calvin-mcd/oceanographer-ec/Project/analog.kicad_sch

## KiCad design Project/analog.kicad_sch (2024-09-16)

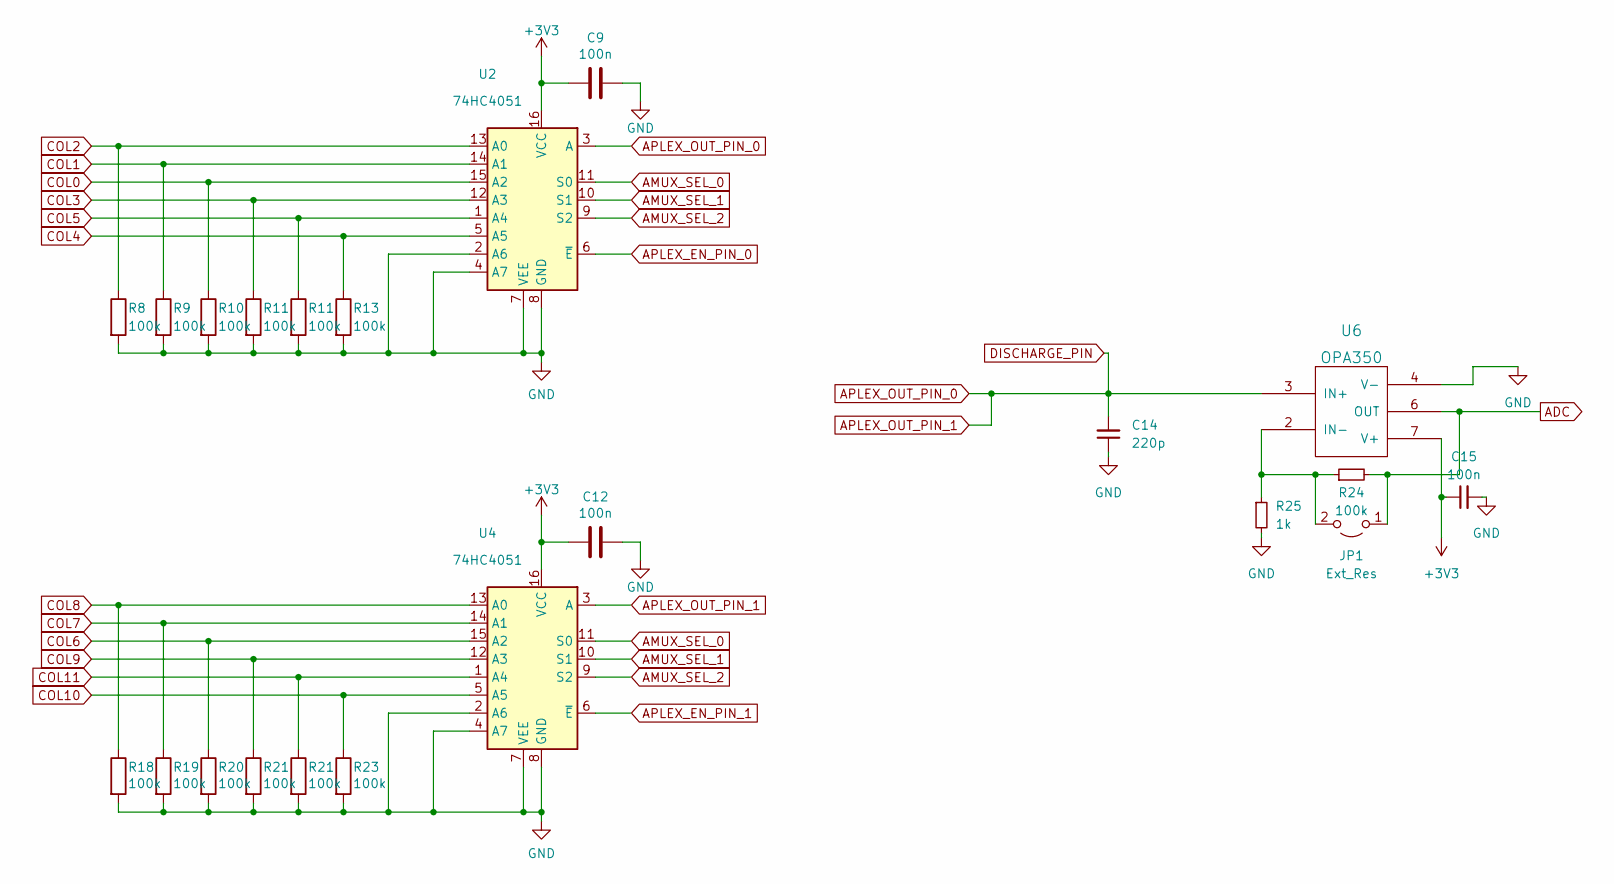
[picture p4: schematic analog.kicad_sch]

Parts:
C9, C12: 100n; C_0402_1005Metric; LCSC C307331
C14: 220p; C_0402_1005Metric
C15: 100n; C_0402_1005Metric
JP1: Ext_Res; R_0603_1608Metric_Pad0.98x0.95mm_HandSolder
R8, R9, R10, R11, R13, R18, R19, R20, R21, R23: 100k; R_0402_1005Metric; LCSC C25741
R24: 100k; R_0402_1005Metric
R25: 1k; R_0402_1005Metric
U2, U4: 74HC4051; TSSOP16; LCSC C5645
U6: OPA350; SOIC-8_3.9x4.9mm_P1.27mm

Connections:
+3V3: C9.2, C12.2, C15.1, U2.16 (VCC), U4.16 (VCC), U6.7 (V+)
ADC: JP1.1 (A), R24.2, U6.6 (OUT)
AMUX_SEL_0: U2.11 (S0), U4.11 (S0)
AMUX_SEL_1: U2.10 (S1), U4.10 (S1)
AMUX_SEL_2: U2.9 (S2), U4.9 (S2)
APLEX_EN_PIN_0: U2.6 (~E)
APLEX_EN_PIN_1: U4.6 (~E)
APLEX_OUT_PIN_0: C14.2, U2.3 (A), U4.3 (A), U6.3 (IN+)
COL0: R10.1, U2.15 (A2)
COL1: R9.1, U2.14 (A1)
COL2: R8.1, U2.13 (A0)
COL3: R11.1, U2.12 (A3)
COL4: R13.1, U2.5 (A5)
COL5: R11.1, U2.1 (A4)
COL6: R20.1, U4.15 (A2)
COL7: R19.1, U4.14 (A1)
COL8: R18.1, U4.13 (A0)
COL9: R21.1, U4.12 (A3)
COL10: R23.1, U4.5 (A5)
COL11: R21.1, U4.1 (A4)
GND: C9.1, C12.1, C14.1, C15.2, R8.2, R9.2, R10.2, R11.2, R13.2, R18.2, R19.2, R20.2, R21.2, R23.2, R25.2, U2.2 (A6), U2.4 (A7), U2.7 (VEE), U2.8 (GND), U4.2 (A6), U4.4 (A7), U4.7 (VEE), U4.8 (GND), U6.4 (V-)
unnamed: JP1.2 (B), R24.1, R25.1, U6.2 (IN-)
