calvin-mcd/oceanographer-ec/Project/ec matrix.kicad_sch

## KiCad design Project/ec matrix.kicad_sch (2024-09-16)

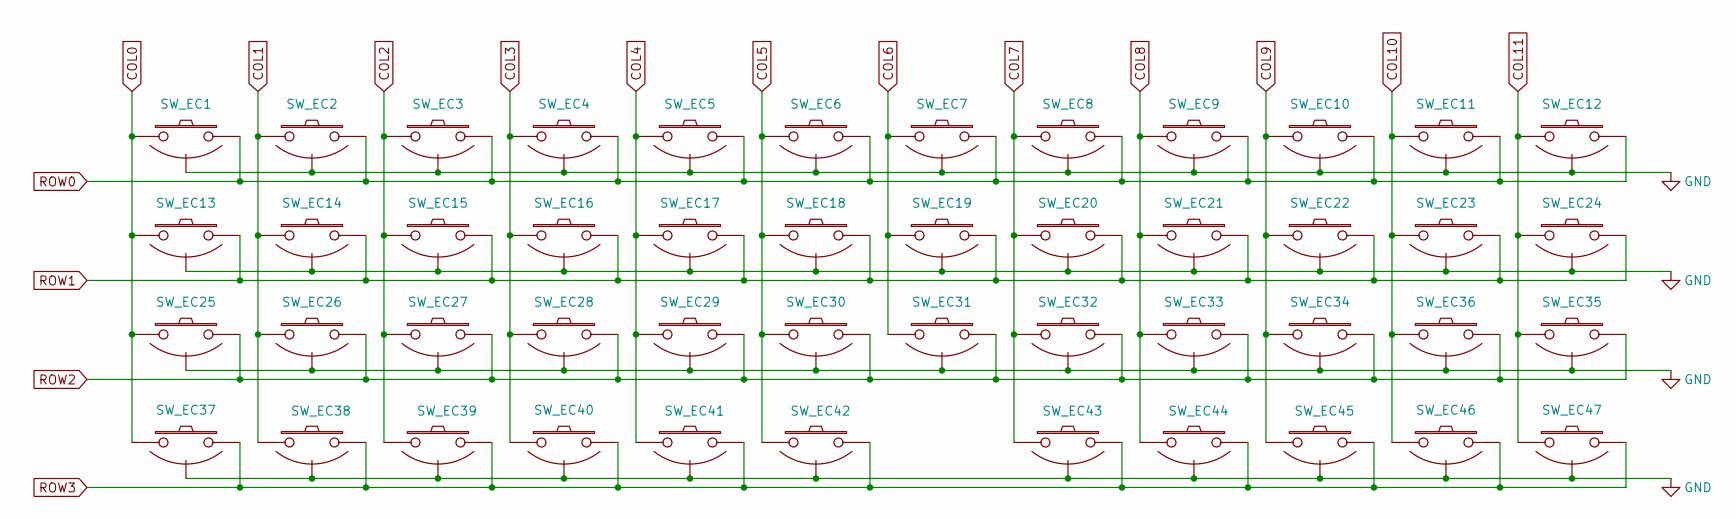
[picture p5: schematic ec matrix.kicad_sch]

Parts:
SW_EC1, SW_EC2, SW_EC3, SW_EC4, SW_EC5, SW_EC6, SW_EC7, SW_EC8, SW_EC9, SW_EC10, SW_EC11, SW_EC12, SW_EC13, SW_EC14, SW_EC15, SW_EC16, SW_EC17, SW_EC18, SW_EC19, SW_EC20, SW_EC21, SW_EC22, SW_EC23, SW_EC24, SW_EC25, SW_EC26, SW_EC27, SW_EC28, SW_EC29, SW_EC30, SW_EC31, SW_EC32, SW_EC33, SW_EC34, SW_EC35, SW_EC36, SW_EC37, SW_EC38, SW_EC39, SW_EC40, SW_EC41, SW_EC42, SW_EC43, SW_EC44, SW_EC45, SW_EC46, SW_EC47: Topre; ecs_pad_1U_no_ring

Connections:
COL0: SW_EC1.1, SW_EC13.1, SW_EC25.1, SW_EC37.1
COL1: SW_EC2.1, SW_EC14.1, SW_EC26.1, SW_EC38.1
COL2: SW_EC3.1, SW_EC15.1, SW_EC27.1, SW_EC39.1
COL3: SW_EC4.1, SW_EC16.1, SW_EC28.1, SW_EC40.1
COL4: SW_EC5.1, SW_EC17.1, SW_EC29.1, SW_EC41.1
COL5: SW_EC6.1, SW_EC18.1, SW_EC30.1, SW_EC42.1
COL6: SW_EC7.1, SW_EC19.1, SW_EC31.1
COL7: SW_EC8.1, SW_EC20.1, SW_EC32.1, SW_EC43.1
COL8: SW_EC9.1, SW_EC21.1, SW_EC33.1, SW_EC44.1
COL9: SW_EC10.1, SW_EC22.1, SW_EC34.1, SW_EC45.1
COL10: SW_EC11.1, SW_EC23.1, SW_EC36.1, SW_EC46.1
COL11: SW_EC12.1, SW_EC24.1, SW_EC35.1, SW_EC47.1
GND: SW_EC1.3 (SG), SW_EC2.3 (SG), SW_EC3.3 (SG), SW_EC4.3 (SG), SW_EC5.3 (SG), SW_EC6.3 (SG), SW_EC7.3 (SG), SW_EC8.3 (SG), SW_EC9.3 (SG), SW_EC10.3 (SG), SW_EC11.3 (SG), SW_EC12.3 (SG), SW_EC13.3 (SG), SW_EC14.3 (SG), SW_EC15.3 (SG), SW_EC16.3 (SG), SW_EC17.3 (SG), SW_EC18.3 (SG), SW_EC19.3 (SG), SW_EC20.3 (SG), SW_EC21.3 (SG), SW_EC22.3 (SG), SW_EC23.3 (SG), SW_EC24.3 (SG), SW_EC25.3 (SG), SW_EC26.3 (SG), SW_EC27.3 (SG), SW_EC28.3 (SG), SW_EC29.3 (SG), SW_EC30.3 (SG), SW_EC31.3 (SG), SW_EC32.3 (SG), SW_EC33.3 (SG), SW_EC34.3 (SG), SW_EC35.3 (SG), SW_EC36.3 (SG), SW_EC37.3 (SG), SW_EC38.3 (SG), SW_EC39.3 (SG), SW_EC40.3 (SG), SW_EC41.3 (SG), SW_EC42.3 (SG), SW_EC43.3 (SG), SW_EC44.3 (SG), SW_EC45.3 (SG), SW_EC46.3 (SG), SW_EC47.3 (SG)
ROW0: SW_EC1.2, SW_EC2.2, SW_EC3.2, SW_EC4.2, SW_EC5.2, SW_EC6.2, SW_EC7.2, SW_EC8.2, SW_EC9.2, SW_EC10.2, SW_EC11.2, SW_EC12.2
ROW1: SW_EC13.2, SW_EC14.2, SW_EC15.2, SW_EC16.2, SW_EC17.2, SW_EC18.2, SW_EC19.2, SW_EC20.2, SW_EC21.2, SW_EC22.2, SW_EC23.2, SW_EC24.2
ROW2: SW_EC25.2, SW_EC26.2, SW_EC27.2, SW_EC28.2, SW_EC29.2, SW_EC30.2, SW_EC31.2, SW_EC32.2, SW_EC33.2, SW_EC34.2, SW_EC35.2, SW_EC36.2
ROW3: SW_EC37.2, SW_EC38.2, SW_EC39.2, SW_EC40.2, SW_EC41.2, SW_EC42.2, SW_EC43.2, SW_EC44.2, SW_EC45.2, SW_EC46.2, SW_EC47.2
