calvin-mcd/oceanographer-ec/Project/mounting holes.kicad_sch

## KiCad design Project/mounting holes.kicad_sch (2024-09-16)

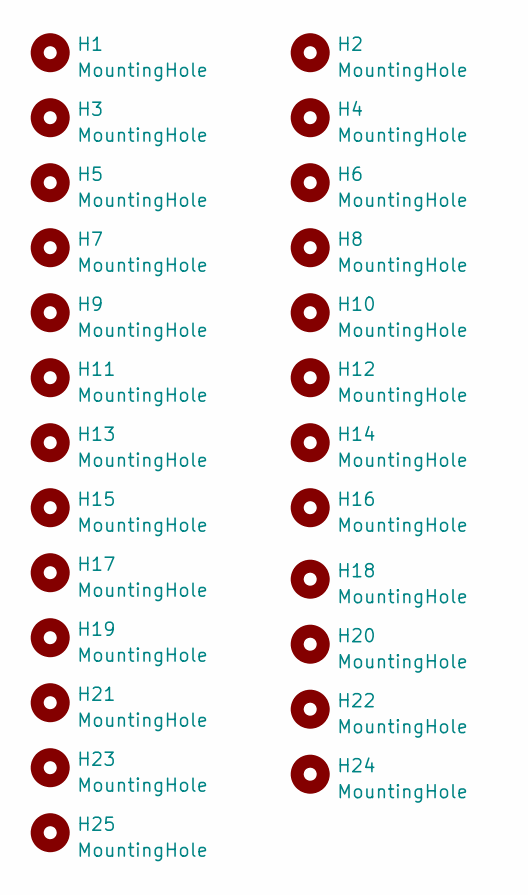
[picture p6: schematic mounting holes.kicad_sch]

Parts:
H1, H2, H3, H4, H5, H6, H7, H8, H9, H10, H11, H12, H13, H14, H15, H16, H17, H18, H19, H20, H21, H22, H23, H24, H25: MountingHole; HOLE_M2
