calvin-mcd/oceanographer-ec/Project/oceanographer EC.kicad_sch

## KiCad design Project/oceanographer EC.kicad_sch (2024-09-16)

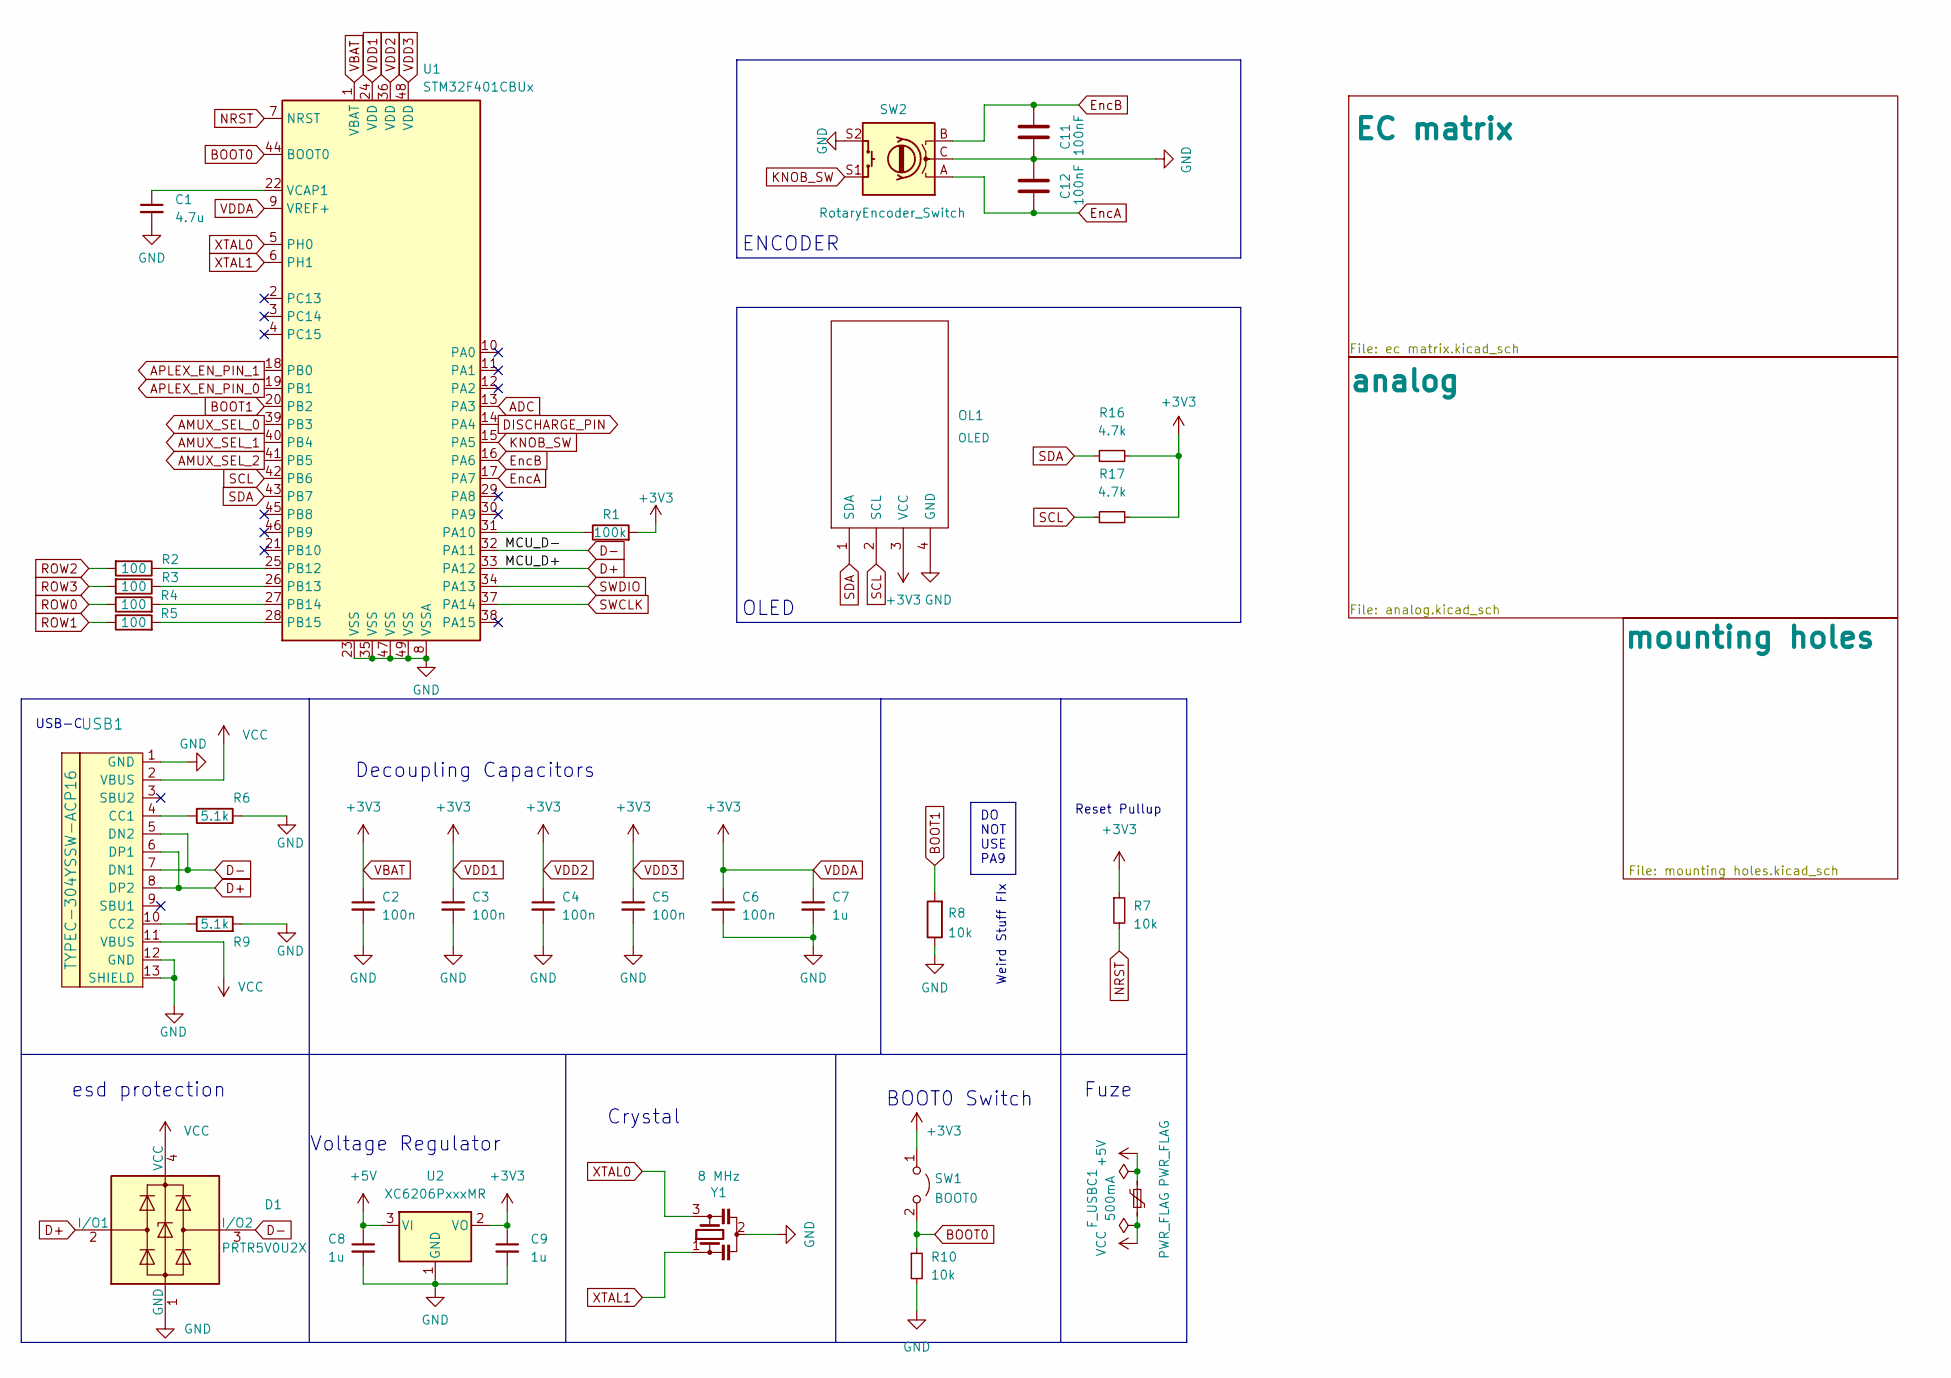
[picture p7: schematic oceanographer EC.kicad_sch]

Parts:
C1: 4.7u; C_0402_1005Metric
C2, C3, C4, C5, C6: 100n; C_0402_1005Metric
C7, C8, C9: 1u; C_0402_1005Metric
C11, C12: 100nF; C_0402_1005Metric; LCSC C307331
D1: PRTR5V0U2X; SOT-143
F_USBC1: 500mA; Fuse_1206_3216Metric
OL1: OLED; OLED_v2
R1: 100k; R_0402_1005Metric; LCSC C25741
R2, R3, R4, R5: 100; R_0402_1005Metric; LCSC C25076
R6, R9: 5.1k; R_0402_1005Metric; LCSC C25905
R7, R10: 10k; R_0402_1005Metric
R8: 10k; R_0402_1005Metric; LCSC C25744
R16, R17: 4.7k; R_0402_1005Metric; LCSC C25900
SW1: BOOT0; PinHeader_1x02_P2.54mm_Vertical
SW2: RotaryEncoder_Switch; ROT_Alps_EC11E-Switch
U1: STM32F401CBUx; QFN-48-1EP_7x7mm_P0.5mm_EP5.6x5.6mm; LCSC C118825
U2: XC6206PxxxMR; SOT-23
USB1: TYPEC-304YSSW-ACP16; HRO-TYPE-C-31-M-12; LCSC C2840392
Y1: 8 MHz; Resonator_SMD_Murata_CSTxExxV-3Pin_3.0x1.1mm; LCSC C907975

Connections:
+3V3: C2.1, C3.1, C4.1, C5.1, C6.1, C7.1, C9.1, OL1.3 (VCC), R1.2, R7.1, R16.2, R17.2, SW1.1 (A), U1.1 (VBAT), U1.9 (VREF+), U1.24 (VDD), U1.36 (VDD), U1.48 (VDD), U2.2 (VO)
+5V: C8.1, F_USBC1.2, U2.3 (VI)
ADC: U1.13 (PA3)
AMUX_SEL_0: U1.39 (PB3)
AMUX_SEL_1: U1.40 (PB4)
AMUX_SEL_2: U1.41 (PB5)
APLEX_EN_PIN_0: U1.19 (PB1)
APLEX_EN_PIN_1: U1.18 (PB0)
BOOT0: R10.1, SW1.2 (B), U1.44 (BOOT0)
BOOT1: R8.2, U1.20 (PB2)
D+: D1.2 (I/O1), U1.33 (PA12), USB1.6 (DP1), USB1.8 (DP2)
D-: D1.3 (I/O2), U1.32 (PA11), USB1.5 (DN2), USB1.7 (DN1)
DISCHARGE_PIN: U1.14 (PA4)
EncA: C12.1, SW2.A, U1.17 (PA7)
EncB: C11.1, SW2.B, U1.16 (PA6)
GND: C1.2, C2.2, C3.2, C4.2, C5.2, C6.2, C7.2, C8.2, C9.2, C11.2, C12.2, D1.1 (GND), OL1.4 (GND), R6.1, R8.1, R9.2, R10.2, SW2.C, SW2.S2, U1.8 (VSSA), U1.23 (VSS), U1.35 (VSS), U1.47 (VSS), U1.49 (VSS), U2.1 (GND), USB1.1 (GND), USB1.12 (GND), USB1.13 (SHIELD), Y1.2
KNOB_SW: SW2.S1, U1.15 (PA5)
NRST: R7.2, U1.7 (NRST)
unnamed: C1.1, U1.22 (VCAP1)
unnamed: R1.1, U1.31 (PA10)
unnamed: R2.1, U1.25 (PB12)
unnamed: R3.1, U1.26 (PB13)
unnamed: R4.2, U1.27 (PB14)
unnamed: R5.2, U1.28 (PB15)
unnamed: R6.2, USB1.4 (CC1)
unnamed: R9.1, USB1.10 (CC2)
ROW0: R4.1
ROW1: R5.1
ROW2: R2.2
ROW3: R3.2
SCL: OL1.2 (SCL), R17.1, U1.42 (PB6)
SDA: OL1.1 (SDA), R16.1, U1.43 (PB7)
SWCLK: U1.37 (PA14)
SWDIO: U1.34 (PA13)
VCC: D1.4 (VCC), F_USBC1.1, USB1.2 (VBUS), USB1.11 (VBUS)
XTAL0: U1.5 (PH0), Y1.3
XTAL1: U1.6 (PH1), Y1.1

Notes on the sheet:
Voltage Regulator
Crystal
ENCODER
Weird Stuff FIx
Fuze
Decoupling Capacitors
OLED
DO NOT USE PA9
esd protection
Reset Pullup
USB-C
BOOT0 Switch
